aditn/18549-Project/Controller/I2CSlave.h

#ifndef I2C_SLAVE_H
#define I2C_SLAVE_H

#include <avr/interrupt.h>
#include <stdint.h>

void I2C_init(uint8_t address);
void I2C_stop(void);
void I2C_setCallbacks(void (*recv)(uint8_t), void (*req)());

static inline void __attribute__((always_inline)) I2C_transmitByte(uint8_t data)
{
  TWDR = data;
}

ISR(TWI_vect);

#endif
