aditn/18549-Project/Controller/uart_test.h

#include <avr/io.h>
#include "defines.h"
#include <stdio.h>

void uart_init(void);
void uart_putchar(char c);
void sendData(float* fData);
extern float fData[NUMBER_OF_SENSORS];

FILE uart_output;
FILE uart_input;
FILE uart_io;
